maarten-pennings/pi1541device/images/qr.png

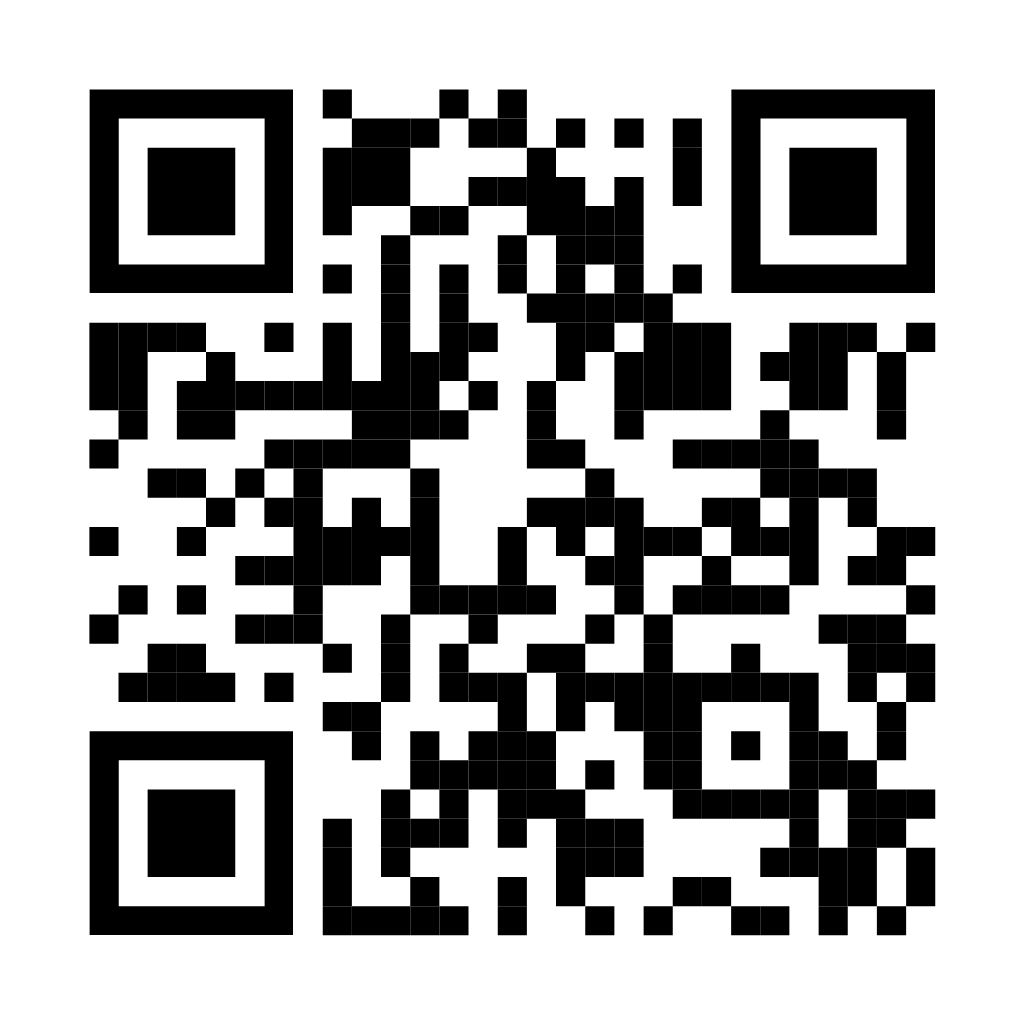
images/qr.png
